probatio/probatio-3dprinting/stls/probatio_block_top_4dof_joystick_v12.stl

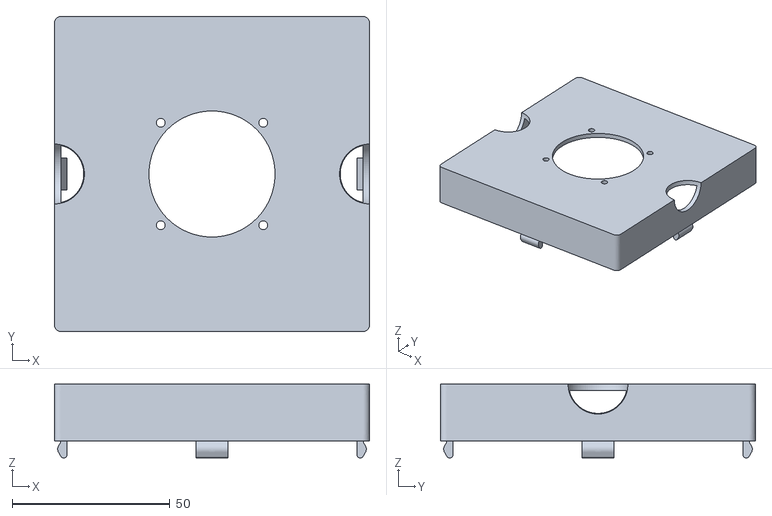
[picture p54: CAD file, 2021-02-25]
stls/probatio_block_top_4dof_joystick_v12.stl
100.0 x 100.0 x 23.4
