probatio/probatio-3dprinting/stls/probatio_hub_case_bottom.stl

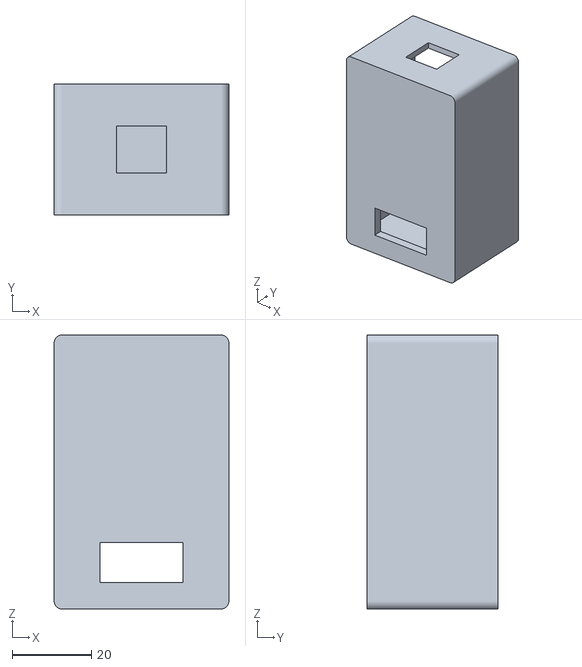
[picture p55: CAD file, 2020-11-27]
stls/probatio_hub_case_bottom.stl
44.0 x 33.0 x 69.0
