probatio/probatio-3dprinting/stls/probatio_hub_case_top.stl

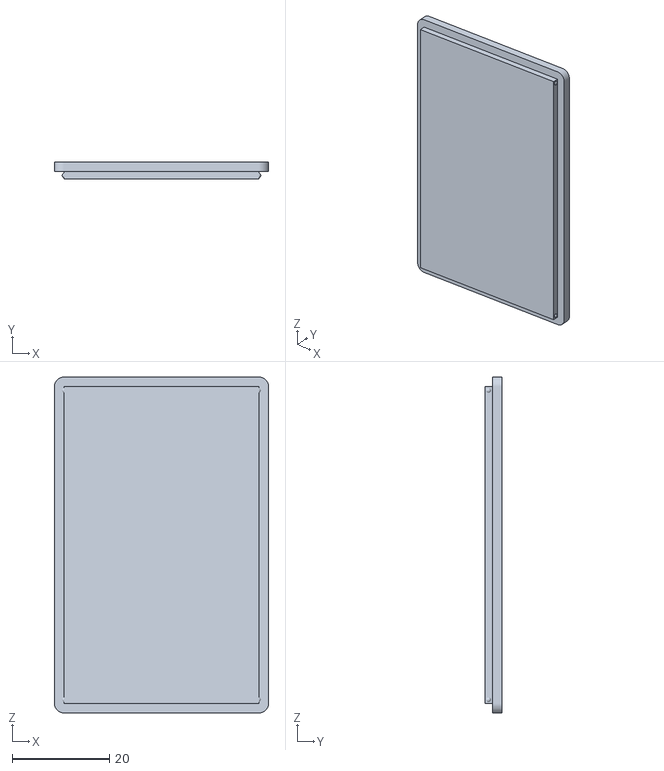
[picture p56: CAD file, 2020-11-27]
stls/probatio_hub_case_top.stl
44.0 x 3.50 x 69.0
