probatio/probatio-3dprinting/stls/probatio_block_top_rotary_encoder_head_crank.stl

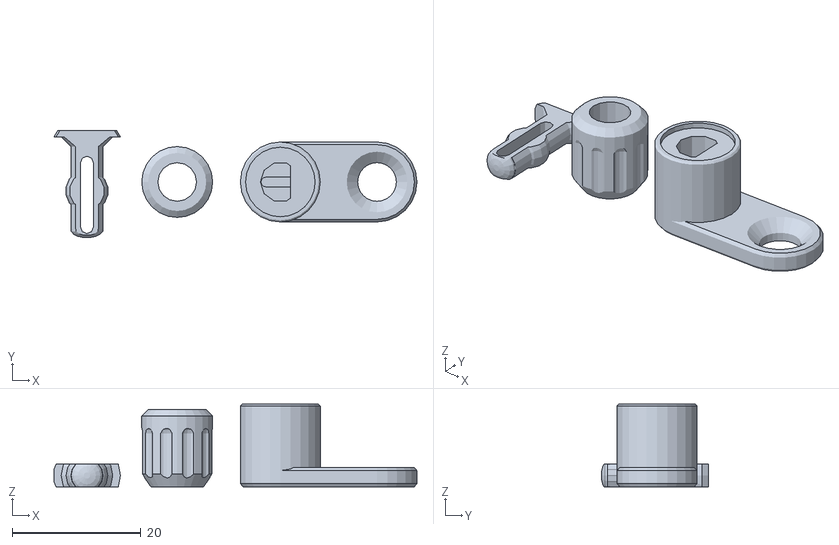
[picture p57: CAD file, 2020-02-09]
stls/probatio_block_top_rotary_encoder_head_crank.stl
56.3 x 16.6 x 12.8
