probatio/probatio-3dprinting/stls/probatio_support_lateral_part_2_v4.stl

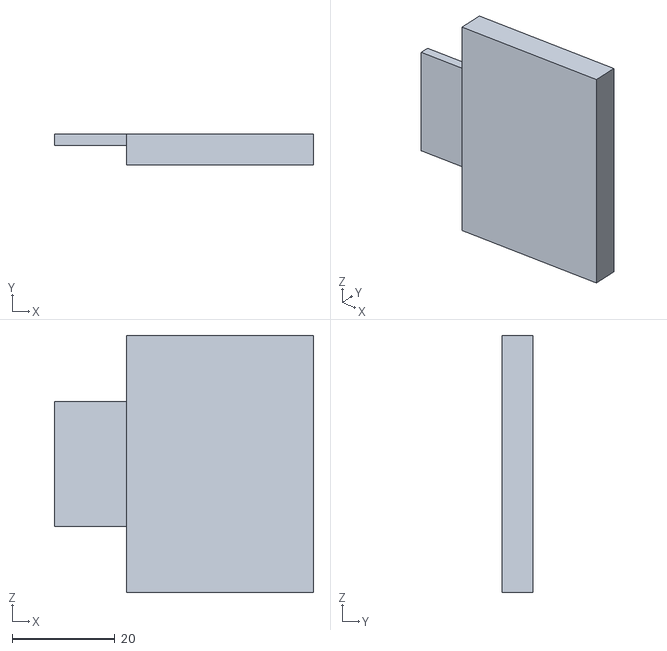
[picture p58: CAD file, 2020-02-09]
stls/probatio_support_lateral_part_2_v4.stl
50.3 x 6.00 x 50.0
