probatio/probatio-3dprinting/stls/probatio_block_top_dual_pistons_cap.stl

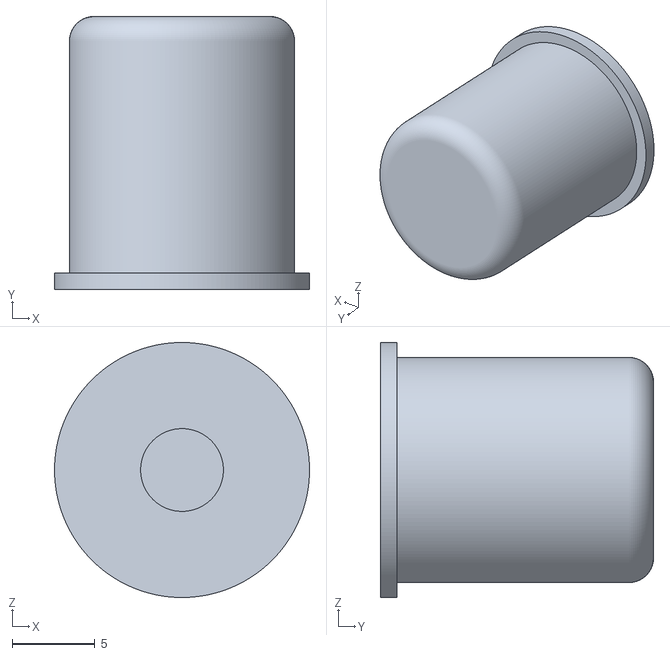
[picture p59: CAD file, 2020-02-09]
stls/probatio_block_top_dual_pistons_cap.stl
15.4 x 16.5 x 15.4
