probatio/probatio-3dprinting/stls/probatio_spacer_block_1x2_bottom_v9.stl

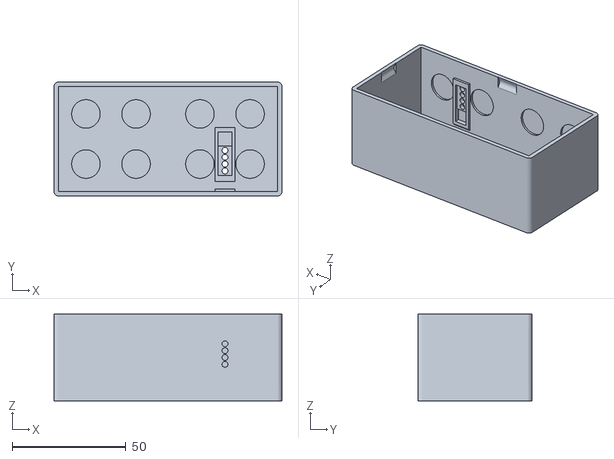
[picture p60: CAD file, 2020-02-09]
stls/probatio_spacer_block_1x2_bottom_v9.stl
100.0 x 50.0 x 38.0
