probatio/probatio-3dprinting/stls/probatio_base_3x3_internal_margin_v17.stl

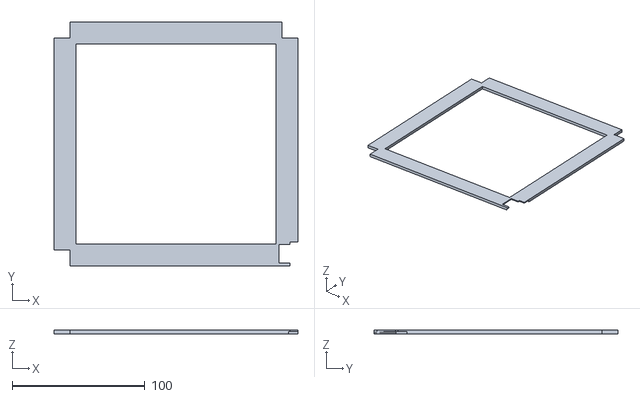
[picture p61: CAD file, 2020-02-09]
stls/probatio_base_3x3_internal_margin_v17.stl
184.0 x 184.0 x 2.75
