probatio/probatio-3dprinting/stls/probatio_base_1x3_bottom_3mm_v9.stl

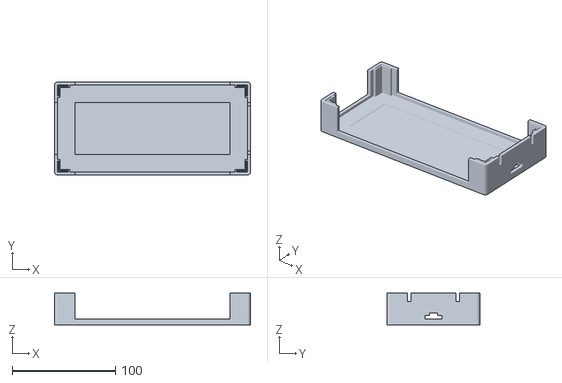
[picture p62: CAD file, 2020-02-09]
stls/probatio_base_1x3_bottom_3mm_v9.stl
190.0 x 90.0 x 31.0
