probatio/probatio-3dprinting/stls/probatio_block_top_dual_pistons.stl

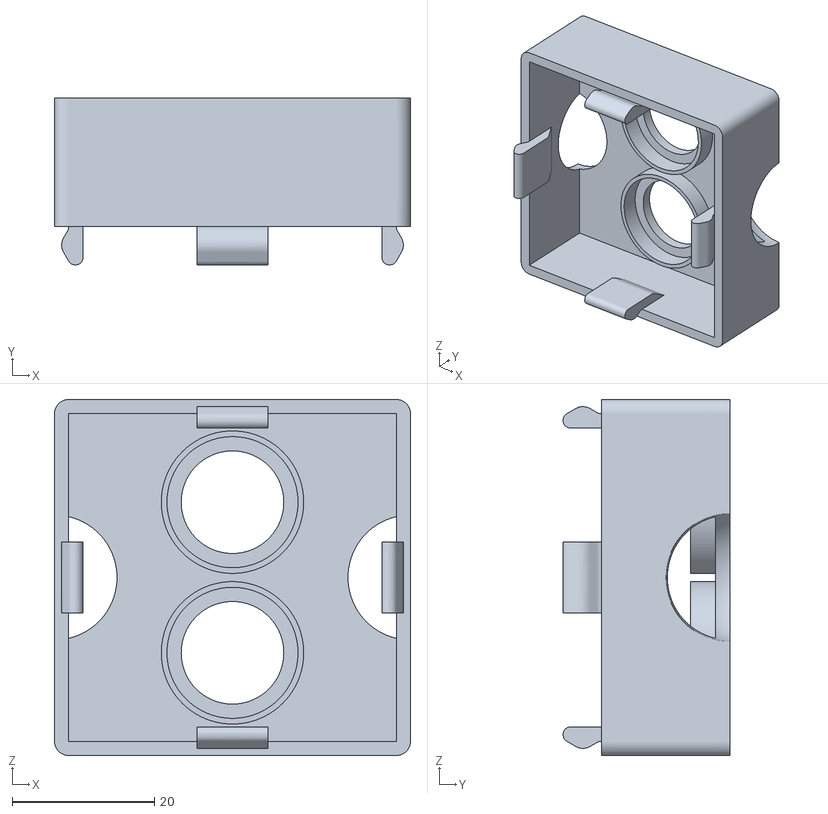
[picture p63: CAD file, 2020-02-09]
stls/probatio_block_top_dual_pistons.stl
50.0 x 23.4 x 50.0
