probatio/probatio-3dprinting/stls/probatio_support_lateral_part_1_v4.stl

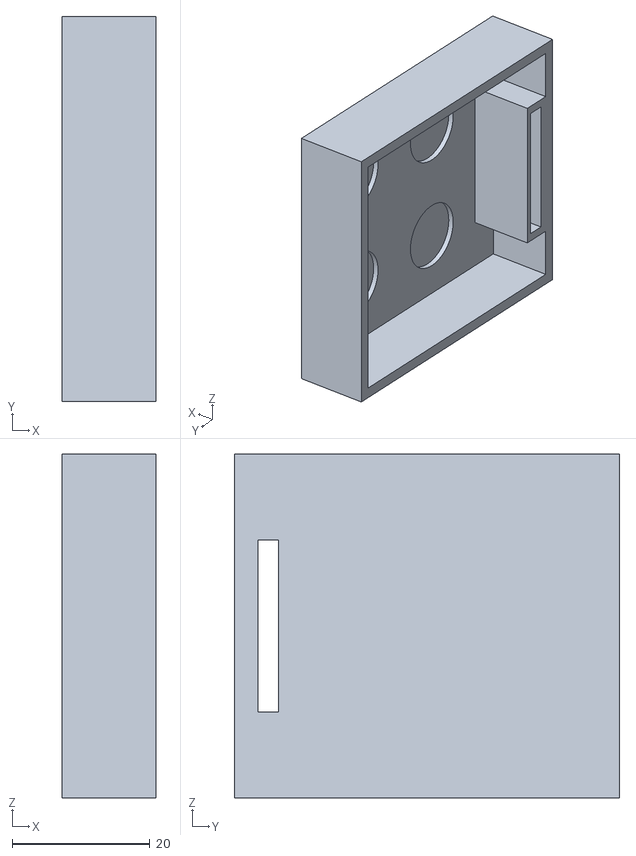
[picture p64: CAD file, 2020-02-09]
stls/probatio_support_lateral_part_1_v4.stl
13.7 x 56.0 x 50.0
