probatio/probatio-3dprinting/stls/probatio_block_top_dual_pistons_cup.stl

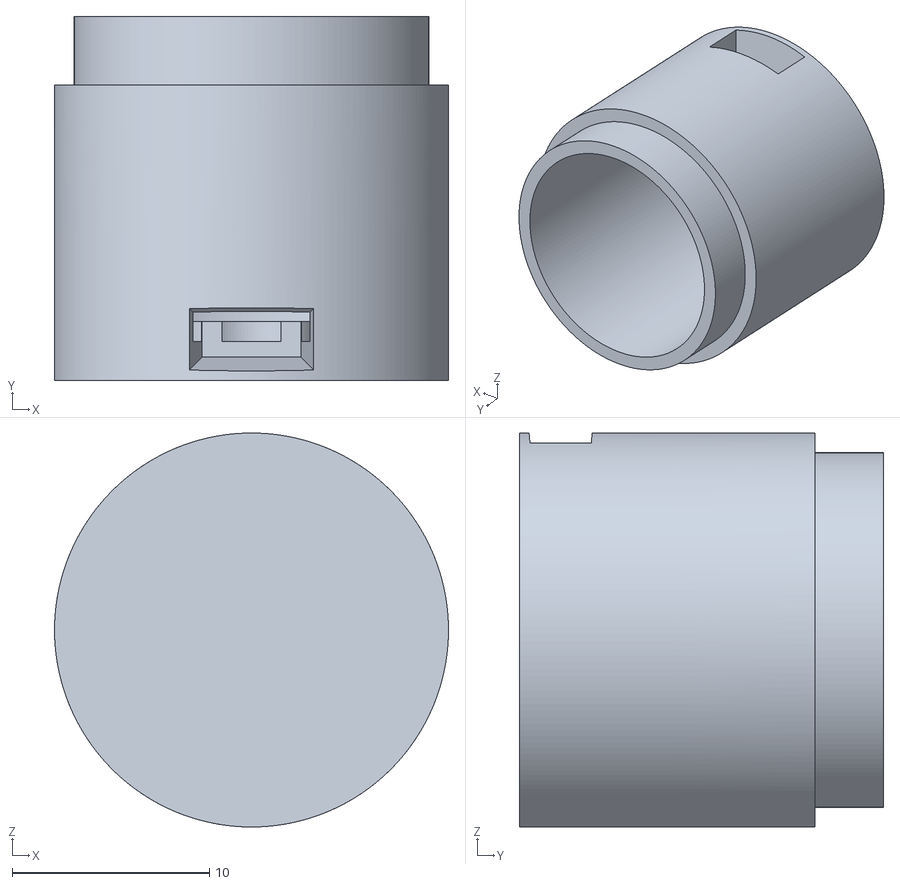
[picture p65: CAD file, 2020-02-09]
stls/probatio_block_top_dual_pistons_cup.stl
20.0 x 18.5 x 20.0
