probatio/probatio-3dprinting/stls/probatio_support_neck_v9.stl

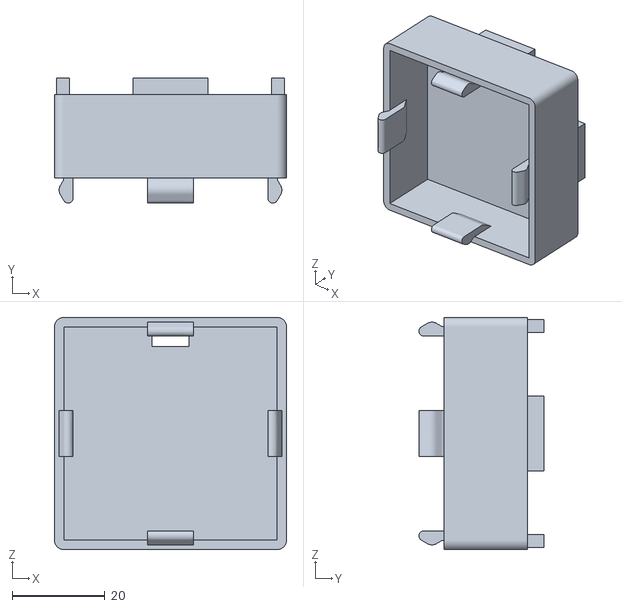
[picture p66: CAD file, 2020-02-09]
stls/probatio_support_neck_v9.stl
50.0 x 26.9 x 50.0
