probatio/probatio-3dprinting/stls/probatio_spacer_block_2x2_top_v9.stl

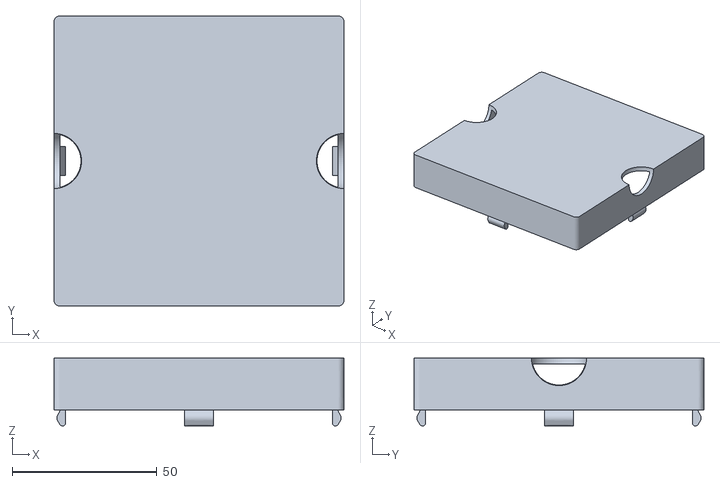
[picture p68: CAD file, 2020-02-09]
stls/probatio_spacer_block_2x2_top_v9.stl
100.0 x 100.0 x 23.4
