probatio/probatio-3dprinting/stls/probatio_support_lateral_single_part_option_v2.stl

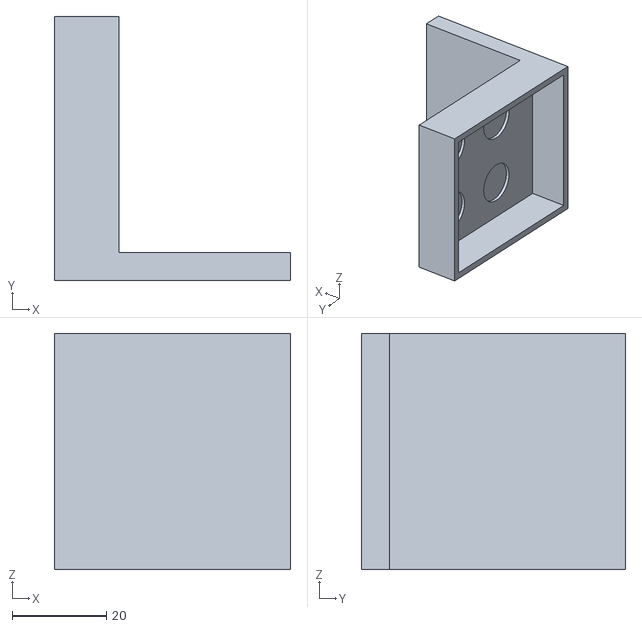
[picture p69: CAD file, 2020-02-09]
stls/probatio_support_lateral_single_part_option_v2.stl
50.0 x 56.0 x 50.0
