probatio/probatio-3dprinting/stls/probatio_base_3x3_top_3mm_v11.stl

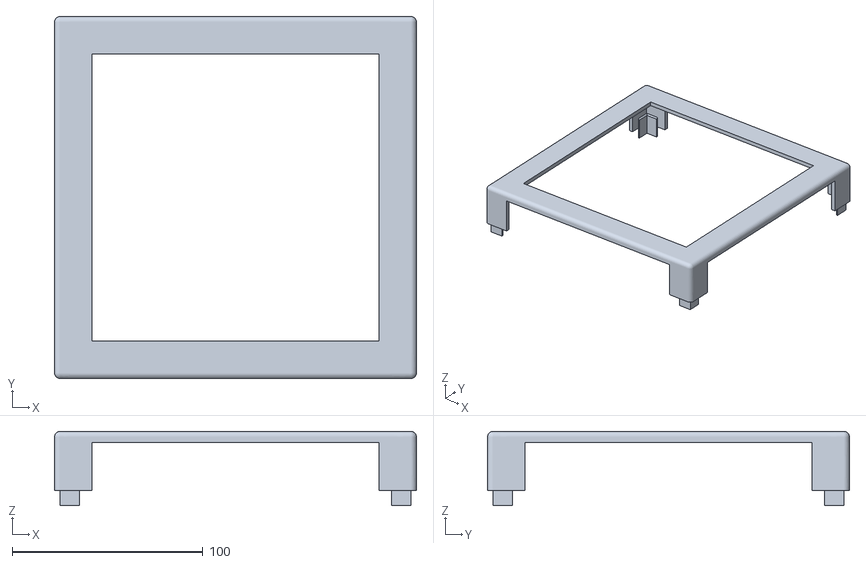
[picture p70: CAD file, 2020-02-09]
stls/probatio_base_3x3_top_3mm_v11.stl
190.0 x 190.0 x 39.0
