probatio/probatio-3dprinting/stls/probatio_base_1x3_internal_margin_v14.stl

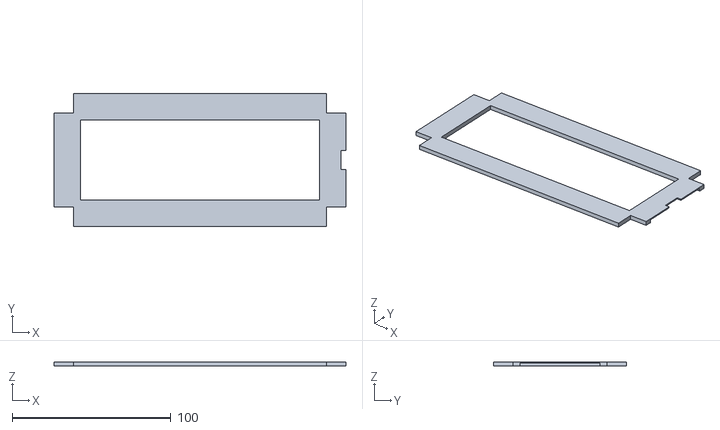
[picture p71: CAD file, 2020-02-09]
stls/probatio_base_1x3_internal_margin_v14.stl
184.0 x 84.0 x 2.80
