probatio/probatio-3dprinting/stls/probatio_base_1x3_top_3mm_v7.stl

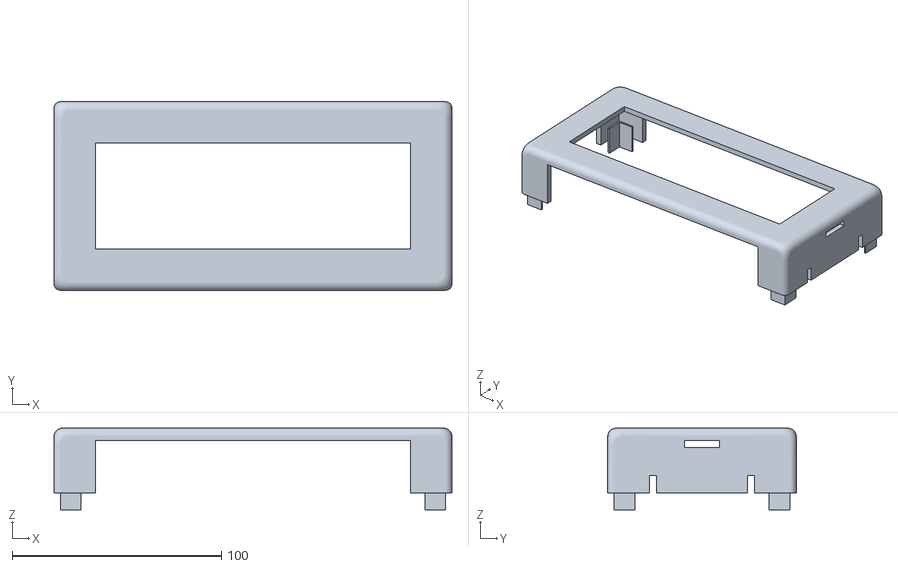
[picture p72: CAD file, 2020-02-09]
stls/probatio_base_1x3_top_3mm_v7.stl
190.0 x 90.0 x 39.0
