probatio/probatio-3dprinting/stls/probatio_spacer_block_1x1_bottom.stl

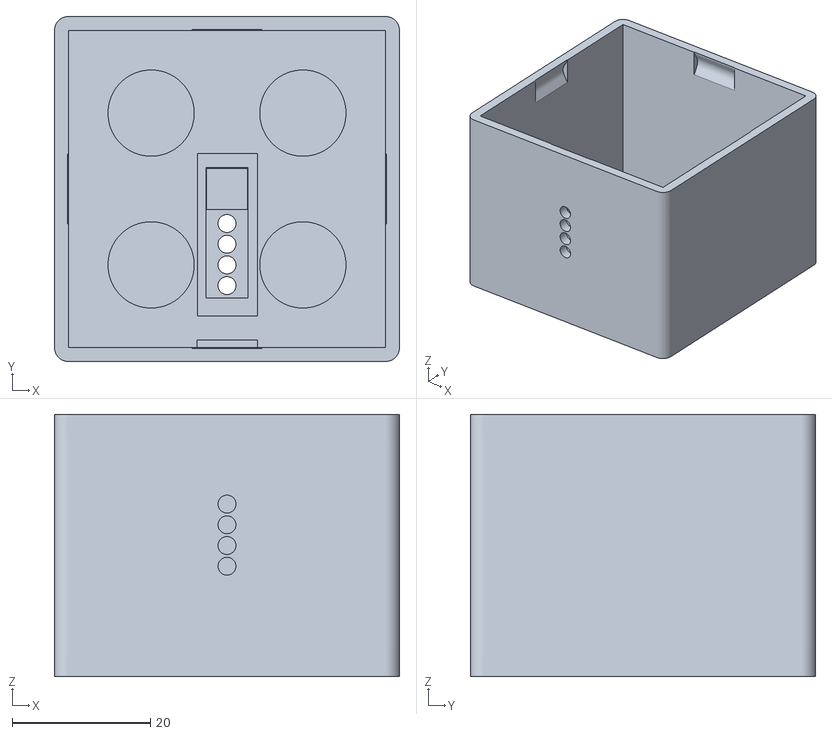
[picture p73: CAD file, 2020-02-09]
stls/probatio_spacer_block_1x1_bottom.stl
50.0 x 50.0 x 38.0
